THARTARUS/ESP32-DEVBOARD/V0_DEVBOARD/3Dfile/DFN-10-1EP_3x3mm_P0.5mm_EP1.55x2.48mm.step

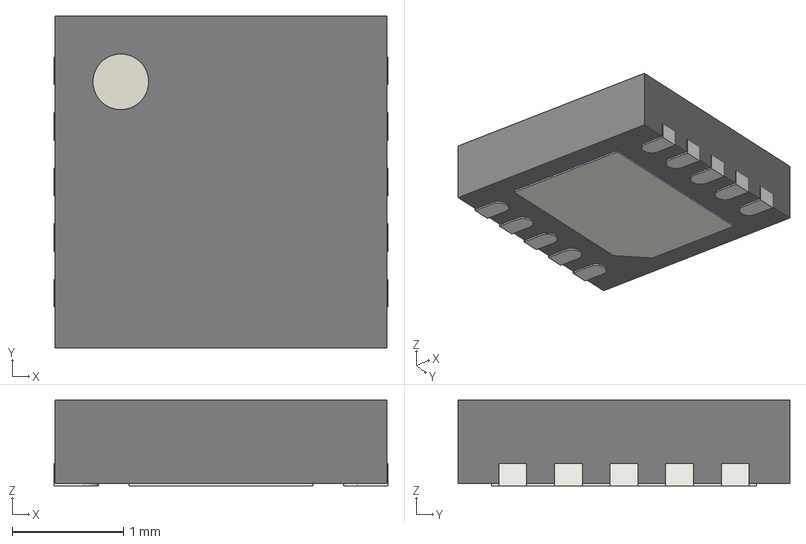
[picture p15: CAD file, 2020-09-09]
V0_DEVBOARD/3Dfile/DFN-10-1EP_3x3mm_P0.5mm_EP1.55x2.48mm.step
3.00 x 2.98 x 0.77 mm
