THARTARUS/ESP32-DEVBOARD/V0_DEVBOARD/3Dfile/12mmx12mm With Green cap.stp

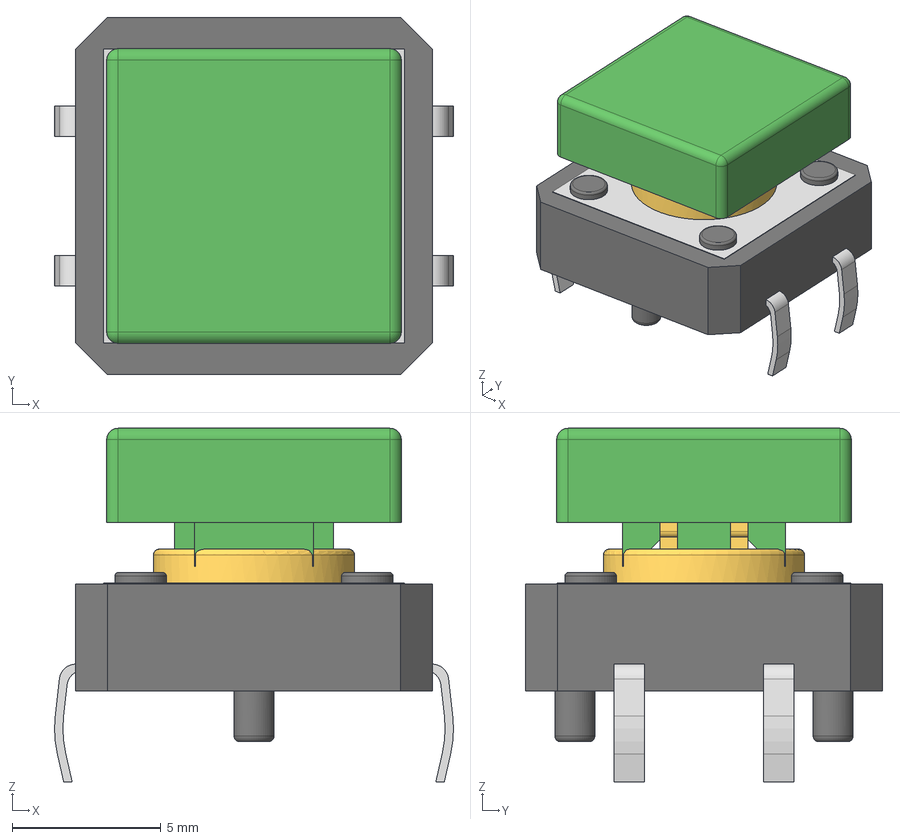
[picture p16: CAD file, 2020-09-09]
V0_DEVBOARD/3Dfile/12mmx12mm With Green cap.stp
13.4 x 12.0 x 11.9 mm
Tactal Switch - THRU(12mmx12mmx__mm)-Square Yellow
12mm Cap
