THARTARUS/ESP32-DEVBOARD/V0_DEVBOARD/3Dfile/AHT20.stp

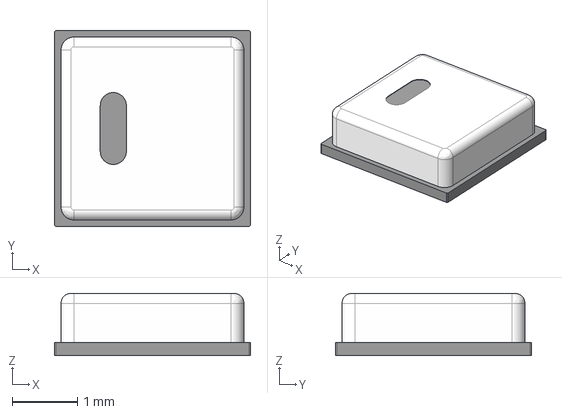
[picture p17: CAD file, 2020-09-09]
V0_DEVBOARD/3Dfile/AHT20.stp
3.00 x 3.00 x 0.95 mm
