THARTARUS/ESP32-DEVBOARD/V0_DEVBOARD/3Dfile/DFN-6 3x3.step

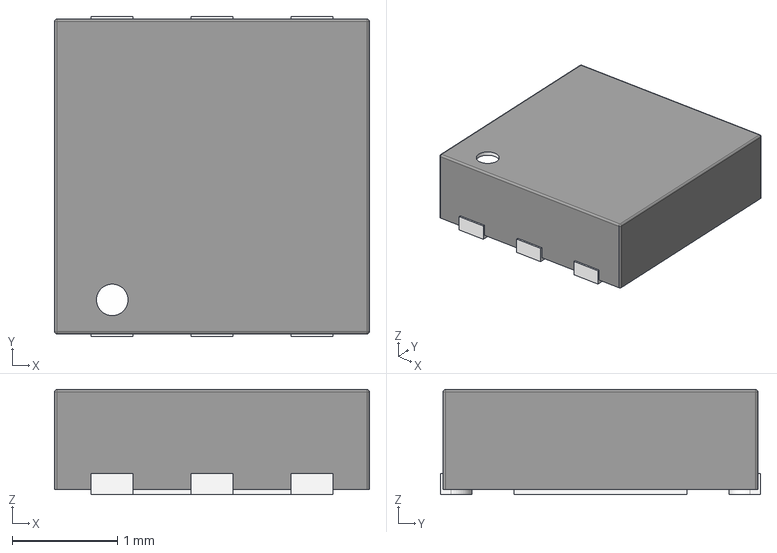
[picture p18: CAD file, 2020-09-09]
V0_DEVBOARD/3Dfile/DFN-6 3x3.step
3.00 x 3.05 x 1.00 mm
