THARTARUS/ESP32-DEVBOARD/V0_DEVBOARD/3Dfile/SW_SPST_PTS645.step

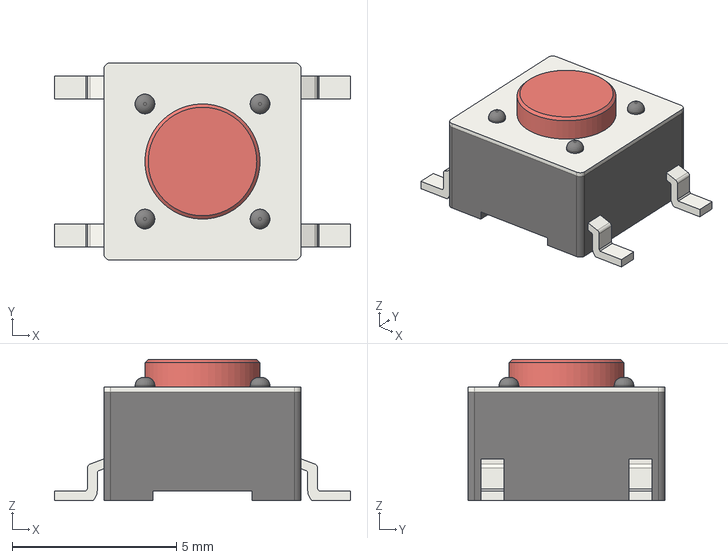
[picture p19: CAD file, 2020-09-09]
V0_DEVBOARD/3Dfile/SW_SPST_PTS645.step
9.00 x 6.00 x 4.30 mm
