THARTARUS/ESP32-DEVBOARD/V0_DEVBOARD/3Dfile/pec12r-2x17f-nxxxx.stp

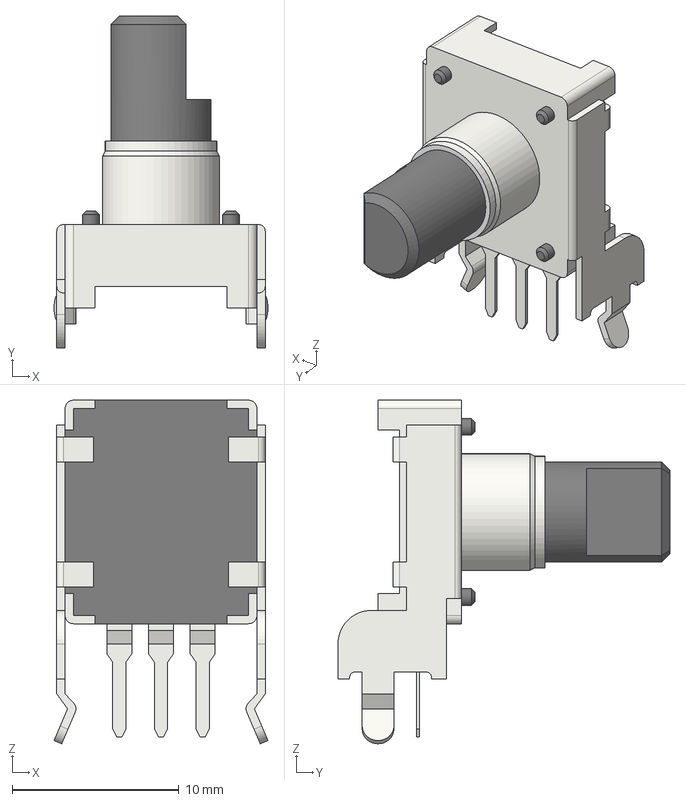
[picture p20: CAD file, 2020-09-09]
V0_DEVBOARD/3Dfile/pec12r-2x17f-nxxxx.stp
12.8 x 19.9 x 20.6 mm
