THARTARUS/ESP32-DEVBOARD/V0_DEVBOARD/3Dfile/SM04B-SRSS-TB(LF)(SN)--3DModel-STEP-56544.STEP

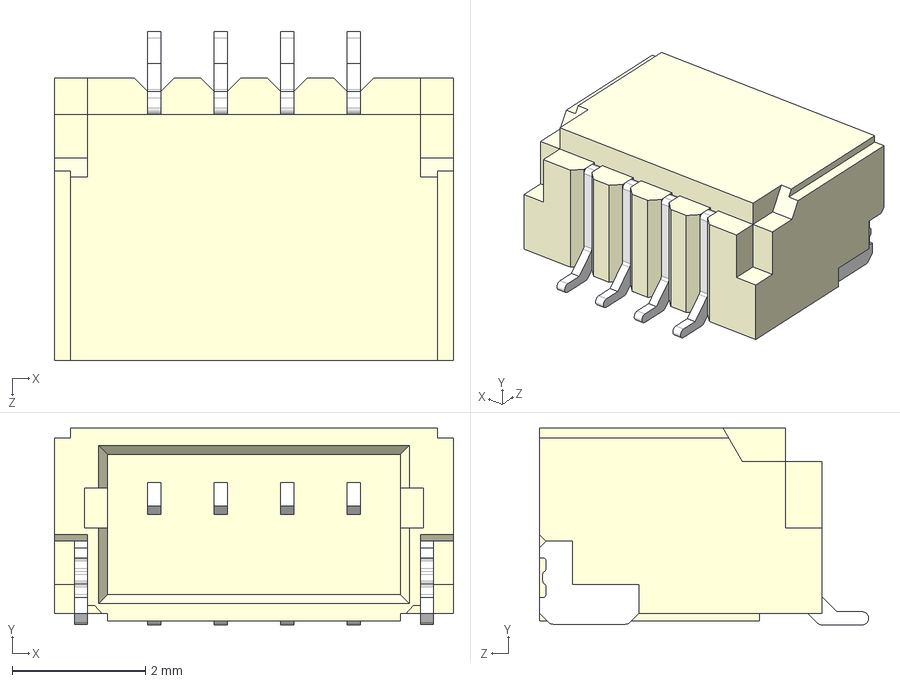
[picture p21: CAD file, 2020-09-09]
V0_DEVBOARD/3Dfile/SM04B-SRSS-TB(LF)(SN)--3DModel-STEP-56544.STEP
6.00 x 2.96 x 4.95 mm
