THARTARUS/ESP32-DEVBOARD/V0_DEVBOARD/3Dfile/bicolor_led.stp

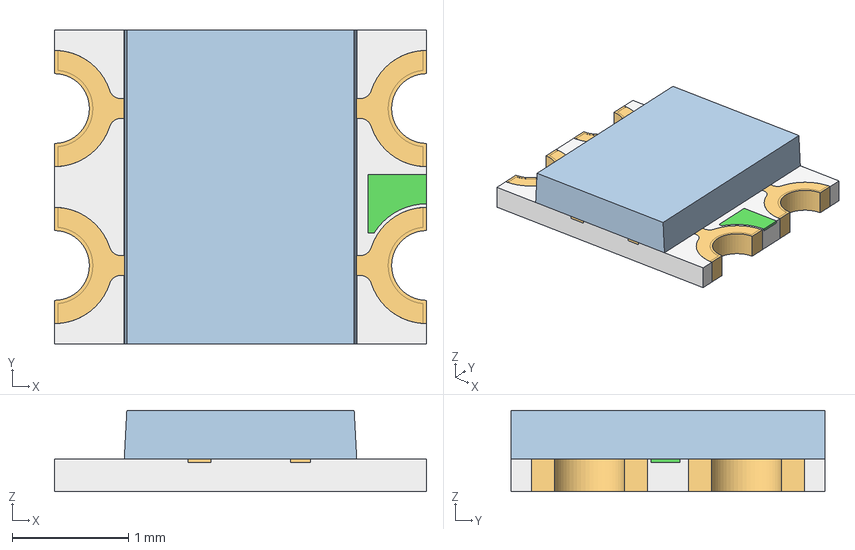
[picture p22: CAD file, 2020-09-09]
V0_DEVBOARD/3Dfile/bicolor_led.stp
3.20 x 2.70 x 0.7 mm
pole x 2
contact x 4
lense
