THARTARUS/ESP32-DEVBOARD/V0_DEVBOARD/3Dfile/PTC1206.stp

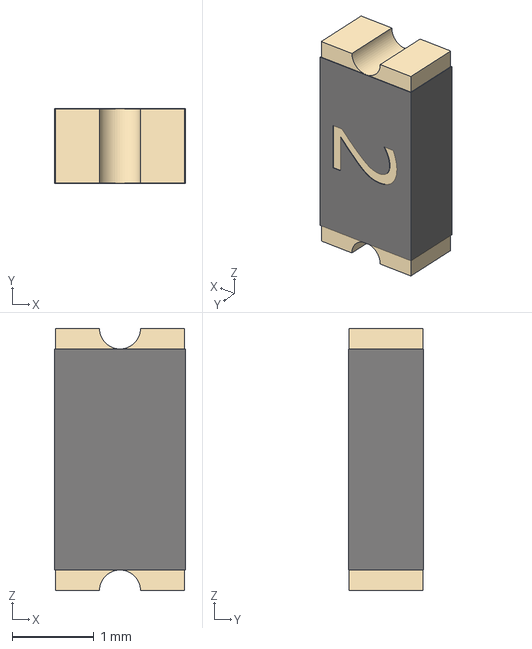
[picture p23: CAD file, 2020-09-09]
V0_DEVBOARD/3Dfile/PTC1206.stp
1.60 x 0.92 x 3.20 mm
