THARTARUS/ESP32-DEVBOARD/V0_DEVBOARD/3Dfile/OLED 2.42 12864 v7.step

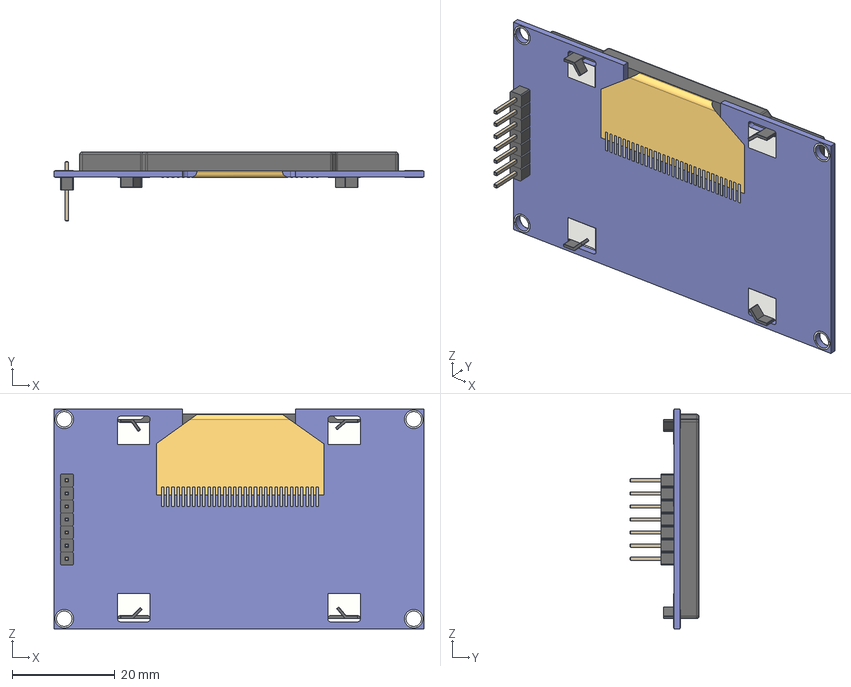
[picture p24: CAD file, 2020-09-09]
V0_DEVBOARD/3Dfile/OLED 2.42 12864 v7.step
72.0 x 13.4 x 42.8 mm
screen
cable
PLS-7 v2
