THARTARUS/ESP32-DEVBOARD/V0_DEVBOARD/3Dfile/suppotoOLED.stp

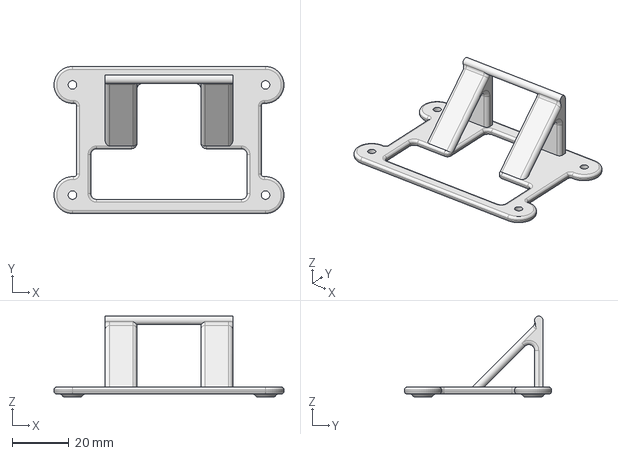
[picture p25: CAD file, 2020-09-09]
V0_DEVBOARD/3Dfile/suppotoOLED.stp
81.0 x 51.8 x 28.5 mm
