THARTARUS/ESP32-DEVBOARD/V0_DEVBOARD/3Dfile/bournsEncoder.dxf

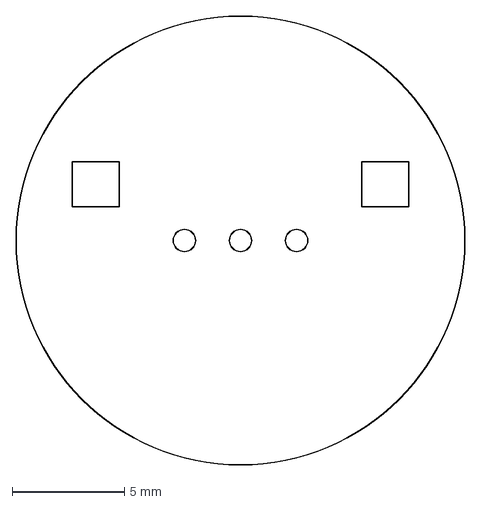
[picture p26: CAD file, 2020-09-09]
V0_DEVBOARD/3Dfile/bournsEncoder.dxf
20.0 x 20.0 mm
