THARTARUS/ESP32-DEVBOARD/V0_DEVBOARD/3Dfile/AB2_HS_40x40x11MM_BLK_WINGS3D.stl

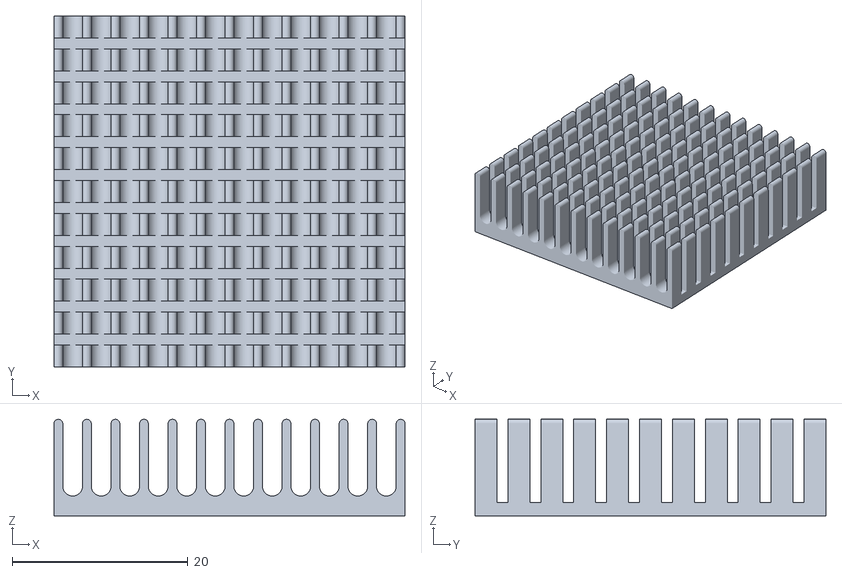
[picture p27: CAD file, 2020-09-09]
V0_DEVBOARD/3Dfile/AB2_HS_40x40x11MM_BLK_WINGS3D.stl
40.0 x 40.0 x 11.0
