THARTARUS/ESP32-DEVBOARD/V0_DEVBOARD/3Dfile/SRR4818A.stp

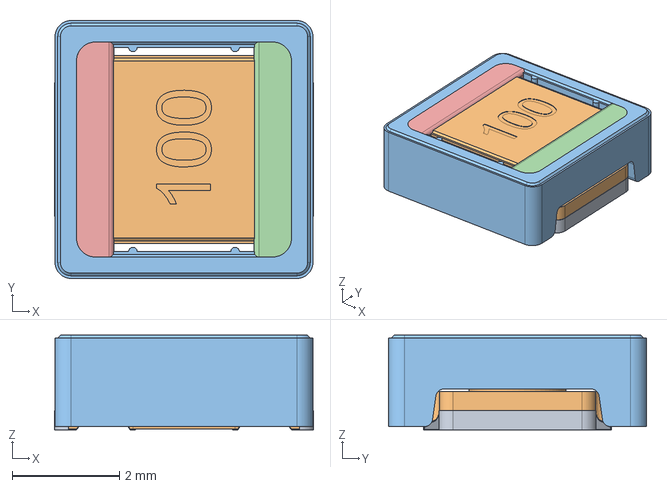
[picture p28: CAD file, 2020-09-09]
V0_DEVBOARD/3Dfile/SRR4818A.stp
4.82 x 4.80 x 1.76 mm
