THARTARUS/ESP32-DEVBOARD/V0_DEVBOARD/3Dfile/Radiator 28x28x20mm.STEP

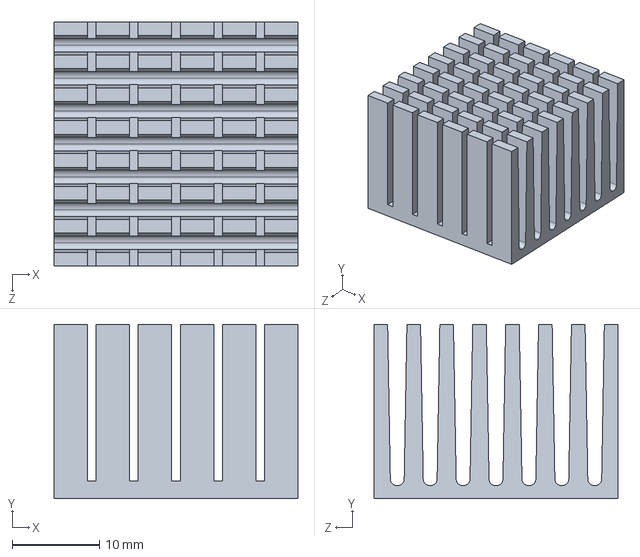
[picture p29: CAD file, 2020-09-09]
V0_DEVBOARD/3Dfile/Radiator 28x28x20mm.STEP
28.0 x 20.0 x 28.0 mm
